probably-Erwins-Cat/Circuit-Nodes/puzzle-pieces/wire-angle_node-voltage/README.MD

# Wire segment — angled (node voltage)

Angled wire segment with a measurement node (banana-jack hole) for convenient voltage measurements using standard 4 mm banana plugs.

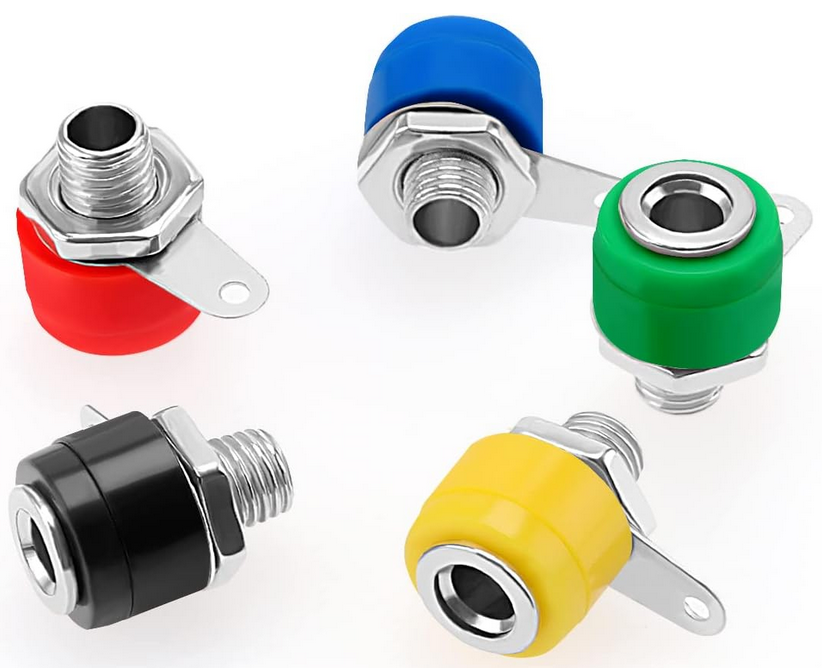
[picture p109: puzzle-pieces/wire-angle_node-voltage/banana-jack-4mm-colored.png]
banana jack
Wire segment top view Wire segment bottom view 

## Typical uses in circuits
- Provide a convenient voltage measurement point at an angled connection.

## Practical notes
- Use color-coded banana plugs to keep wiring clear and consistent for students.
