probably-Erwins-Cat/Circuit-Nodes/puzzle-pieces/end-node-single_blank/README.MD

# Blank End Node

This puzzle piece is an unlabeled connector that can serve multiple functions in a circuit. It features an M6-sized hole where a banana plug terminal can be screwed in, allowing flexible use depending on your circuit's needs.

Circuit Diagram Circuit Diagram Circuit Diagram
