probably-Erwins-Cat/Circuit-Nodes/printable-bases/print-time-twenty-printable-bases.png

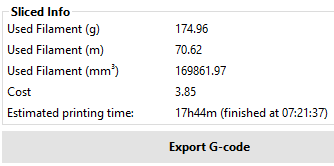
printable-bases/print-time-twenty-printable-bases.png
