probably-Erwins-Cat/Circuit-Nodes/puzzle-pieces/component_resistor_SMT_with-printed-value/component_resistor_SMT_with-printed-value.kicad_pcb

## KiCad design puzzle-pieces/component_resistor_SMT_with-printed-value/component_resistor_SMT_with-printed-value.kicad_pcb (2025-12-11)

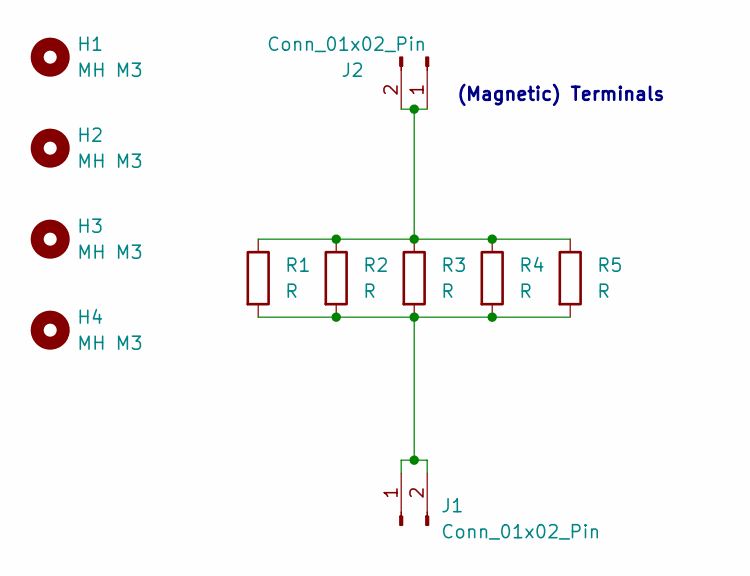
[picture p158: schematic component_resistor_SMT_with-printed-value.kicad_sch]

Parts:
H1, H2, H3, H4: MH M3; MountingHole_3.0mm_M3_tight
J1, J2: Conn_01x02_Pin; Magentic_Connector_1x02_P2.5mm_Horizontal
R1: R; R_2512_6332Metric
R2: R; R_2010_5025Metric
R3: R; R_1210_3225Metric
R4: R; R_1206_3216Metric
R5: R; R_0805_2012Metric

Connections:
unnamed: J2.1, J2.2, R1.1, R2.1, R3.1, R4.1, R5.1
NordSued: J1.1, J1.2, R1.2, R2.2, R3.2, R4.2, R5.2

Notes on the sheet:
(Magnetic) Terminals

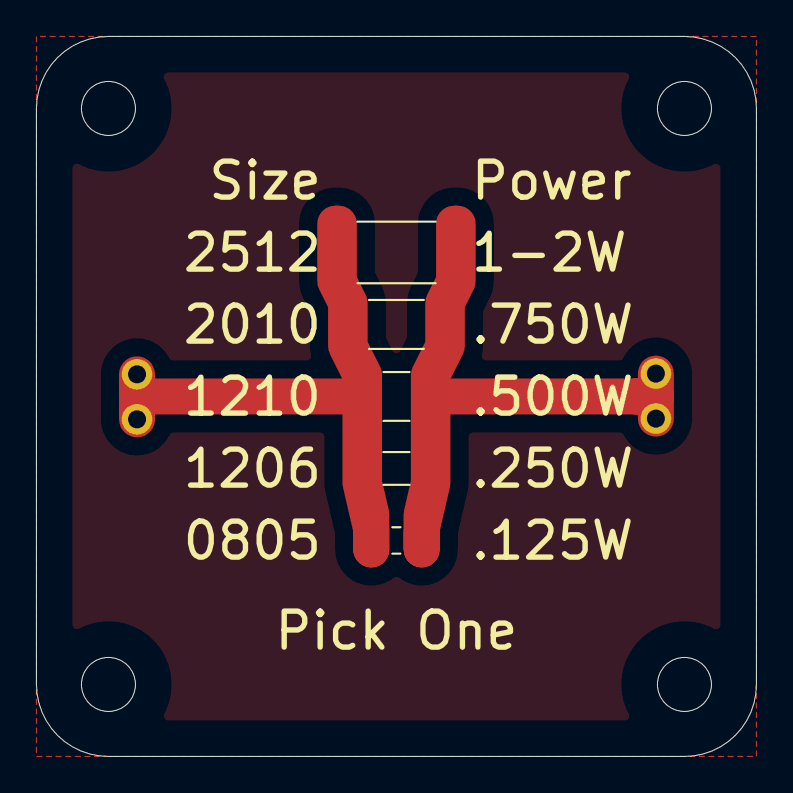
[picture p159: board component_resistor_SMT_with-printed-value.kicad_pcb from above]

Board: 2 copper layers, 40.0 x 40.0 mm, 11 parts (0 on the bottom side), 2 nets.
