probably-Erwins-Cat/Circuit-Nodes/puzzle-pieces/component_resistor_SMT_top-mount/component_resistor_SMT_top-mount.kicad_pcb

## KiCad design puzzle-pieces/component_resistor_SMT_top-mount/component_resistor_SMT_top-mount.kicad_pcb (2025-12-11)

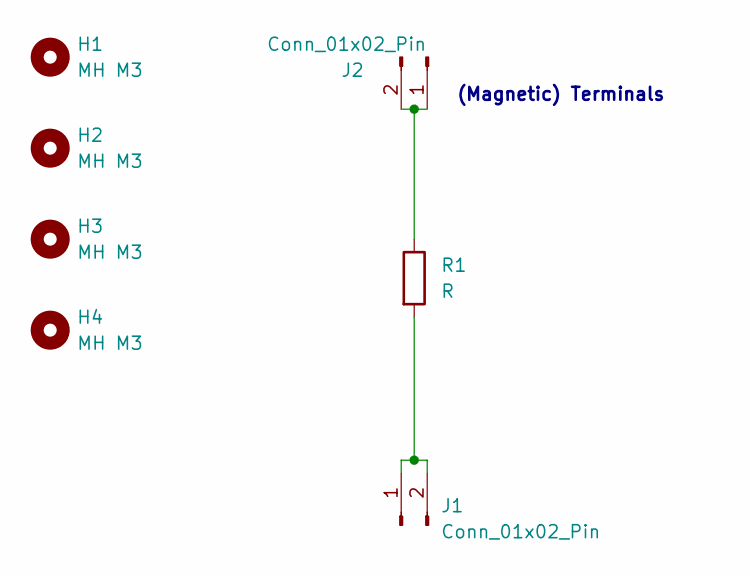
[picture p160: schematic component_resistor_SMT_top-mount.kicad_sch]

Parts:
H1, H2, H3, H4: MH M3; MountingHole_3.0mm_M3_tight
J1, J2: Conn_01x02_Pin; Magentic_Connector_1x02_P2.5mm_Horizontal
R1: R; R_2512_6332Metric_Pad1.40x3.35mm_HandSolder

Connections:
unnamed: J1.1, J1.2, R1.2
unnamed: J2.1, J2.2, R1.1

Notes on the sheet:
(Magnetic) Terminals

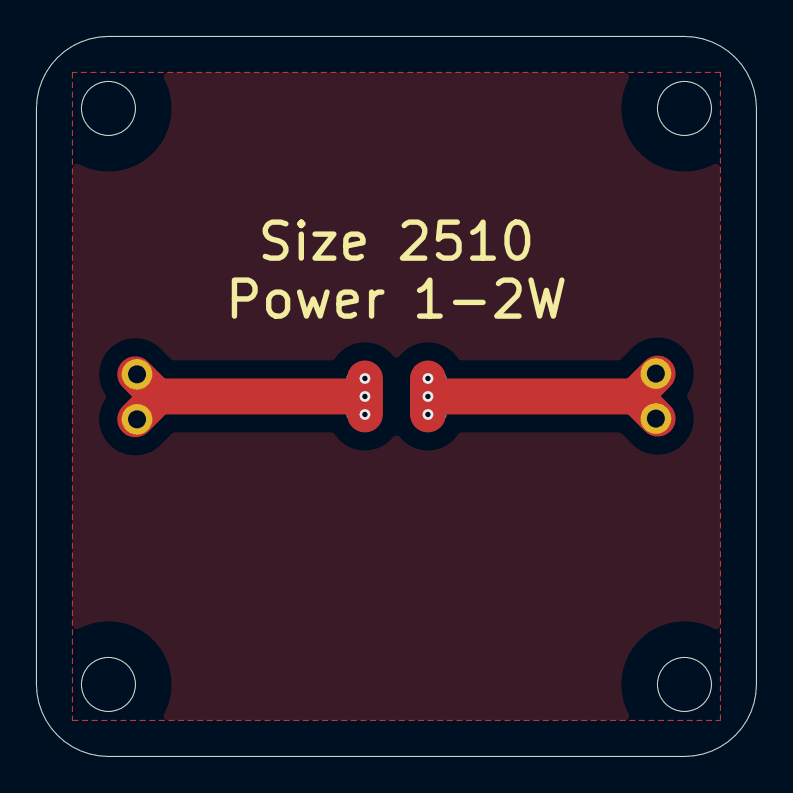
[picture p161: board component_resistor_SMT_top-mount.kicad_pcb from above]

Board: 2 copper layers, 40.0 x 40.0 mm, 7 parts (1 on the bottom side), 2 nets.
