probably-Erwins-Cat/Circuit-Nodes/puzzle-pieces/component_potentiometer_high-power/component_potentiometer_high-power.kicad_pcb

## KiCad design puzzle-pieces/component_potentiometer_high-power/component_potentiometer_high-power.kicad_pcb (2025-12-11)

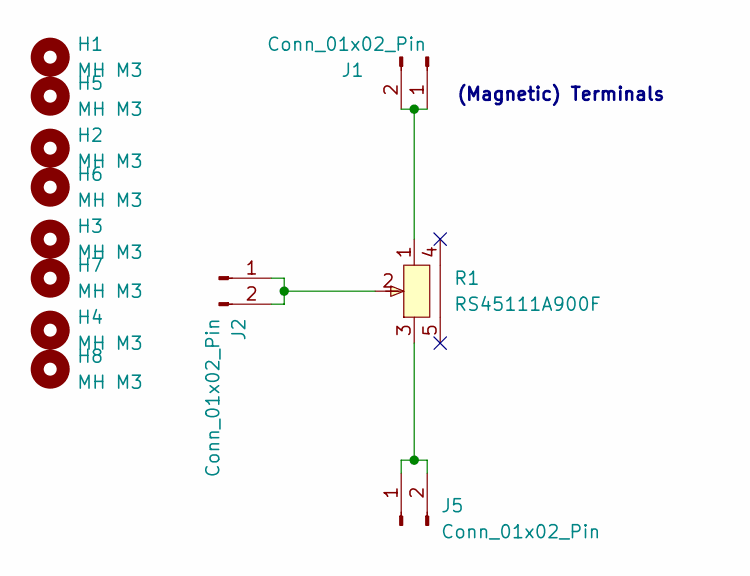
[picture p162: schematic component_potentiometer_high-power.kicad_sch]

Parts:
H1, H2, H3, H4, H5, H6, H7, H8: MH M3; MountingHole_3.0mm_M3_tight
J1, J2, J5: Conn_01x02_Pin; Magentic_Connector_1x02_P2.5mm_Horizontal
R1: RS45111A900F; RES-ADJ-THT-High-Power-Conrad; LCSC Part C370991

Connections:
unnamed: J1.1, J1.2, R1.1
unnamed: J2.1, J2.2, R1.2
unnamed: J5.1, J5.2, R1.3

Notes on the sheet:
(Magnetic) Terminals

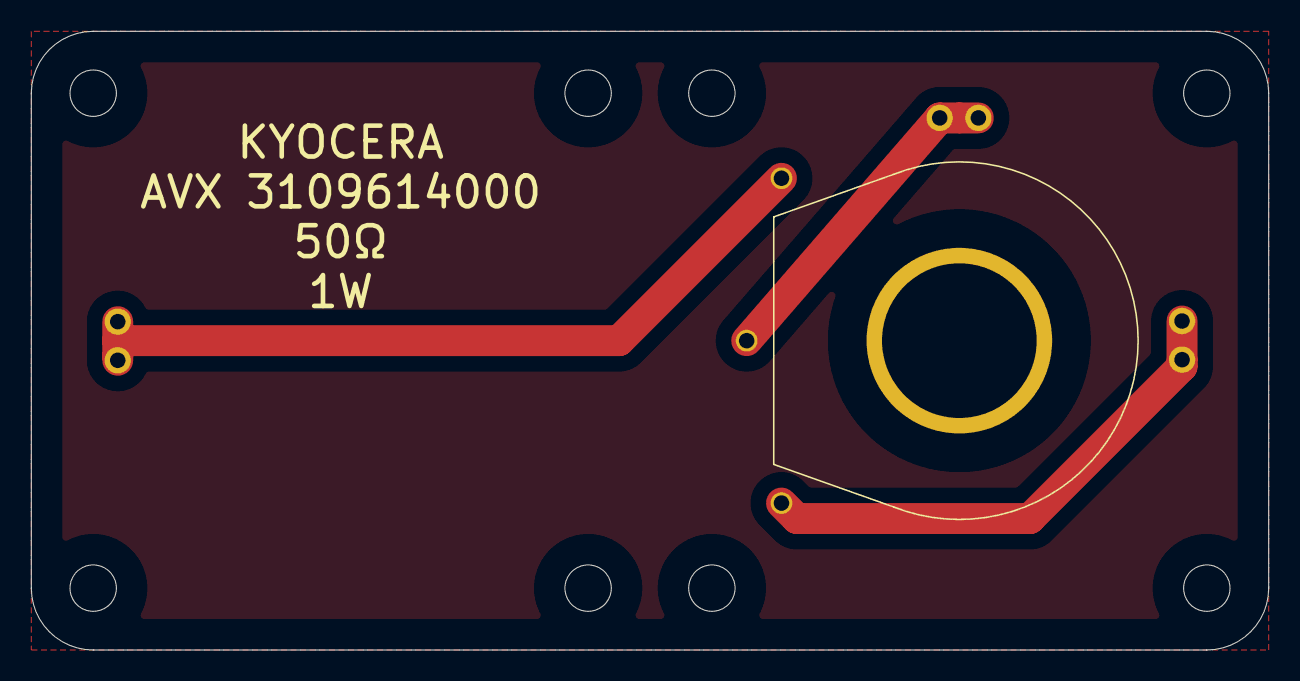
[picture p163: board component_potentiometer_high-power.kicad_pcb from above]

Board: 2 copper layers, 80.0 x 40.0 mm, 12 parts (1 on the bottom side), 3 nets.
