probably-Erwins-Cat/Circuit-Nodes/puzzle-pieces/component_charge-pump-inverter/component_charge-pump-inverter.kicad_pcb

## KiCad design puzzle-pieces/component_charge-pump-inverter/component_charge-pump-inverter.kicad_pcb (2025-12-05)

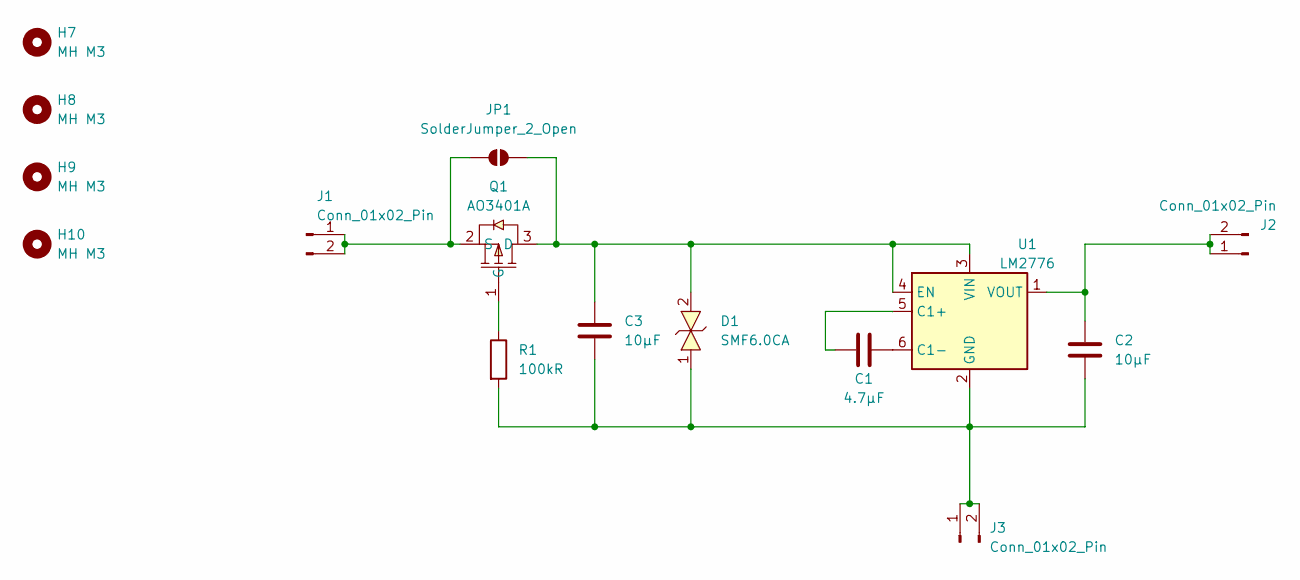
[picture p164: schematic component_charge-pump-inverter.kicad_sch]

Parts:
C1: 4.7µF; C_0805_2012Metric_Pad1.18x1.45mm_HandSolder
C2, C3: 10µF; C_0805_2012Metric_Pad1.18x1.45mm_HandSolder; LCSC C15850
D1: SMF6.0CA; SOD-123FL_L2.8-W1.8-LS3.7-BI; LCSC Part C2836402
H7, H8, H9, H10: MH M3; MountingHole_3.0mm_M3_tight
J1, J2, J3: Conn_01x02_Pin; Magnetic_Connector_1x02_P2.5mm_Horizontal_round-ears
JP1: SolderJumper_2_Open; SolderJumper-2_P1.3mm_Open_RoundedPad1.0x1.5mm
Q1: AO3401A; SOT-23-3_L2.9-W1.6-P1.90-LS2.8-BR; LCSC Part C5224202
R1: 100kR; R_0805_2012Metric_Pad1.20x1.40mm_HandSolder; LCSC C149504
U1: LM2776; SOT-23-6; LCSC C69527

Connections:
unnamed: J1.1, J1.2, JP1.1 (A), Q1.2 (S)
unnamed: C2.1, J2.1, J2.2, U1.1 (VOUT)
unnamed: C2.2, C3.2, D1.1, J3.1, J3.2, R1.2, U1.2 (GND)
unnamed: C3.1, D1.2, JP1.2 (B), Q1.3 (D), U1.3 (VIN), U1.4 (EN)
unnamed: Q1.1 (G), R1.1
unnamed: C1.1, U1.5 (C1+)
unnamed: C1.2, U1.6 (C1-)

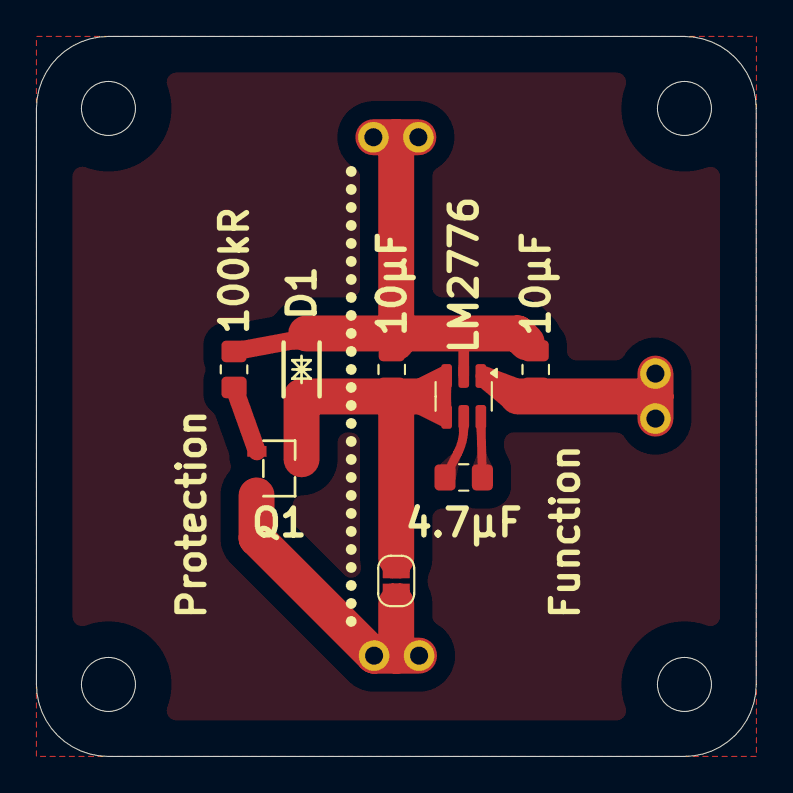
[picture p165: board component_charge-pump-inverter.kicad_pcb from above]

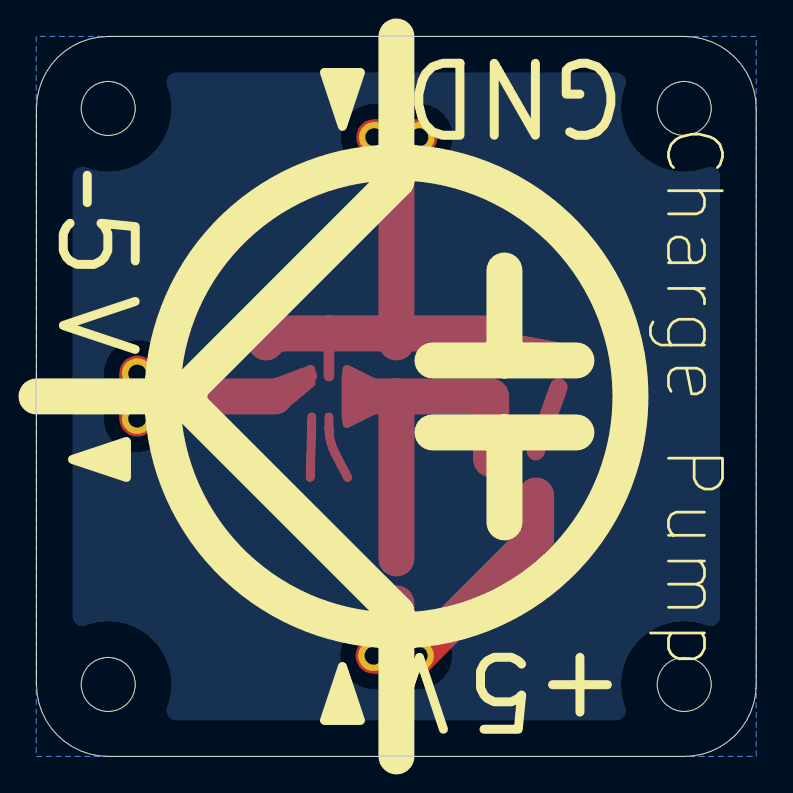
[picture p166: board component_charge-pump-inverter.kicad_pcb from below]

Board: 2 copper layers, 40.0 x 40.0 mm, 15 parts (4 on the bottom side), 7 nets.
